mikulski-lab/C25953-emmu/gal22v10/graphics/mmu_22v10_wiring.png

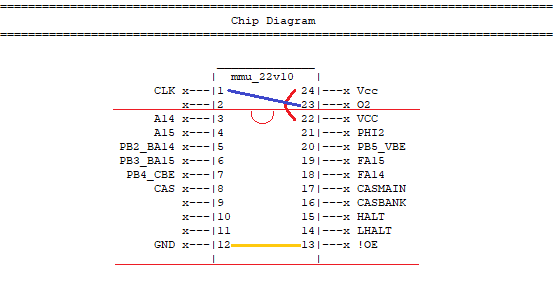
gal22v10/graphics/mmu_22v10_wiring.png
